mrdean05/smart-pos/images/image3.png

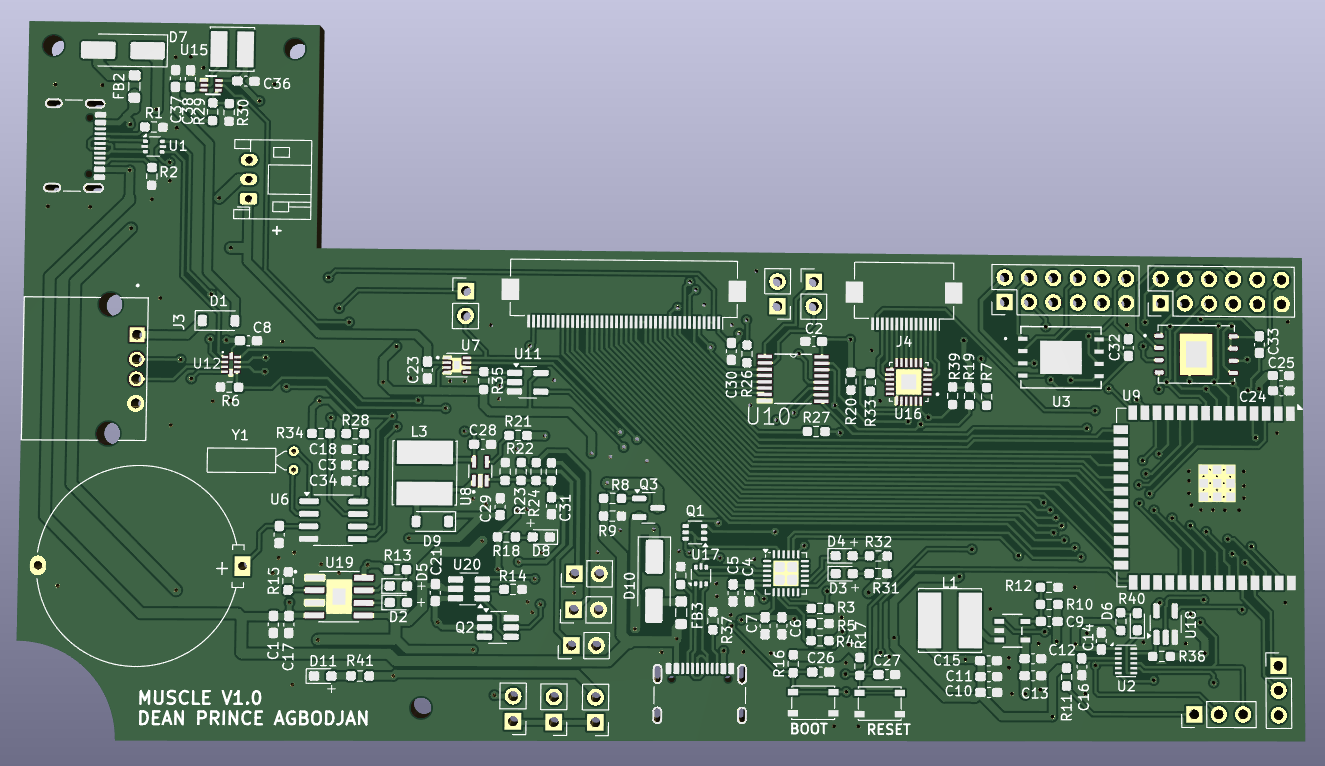
images/image3.png
