mrdean05/smart-pos/images/image5.png

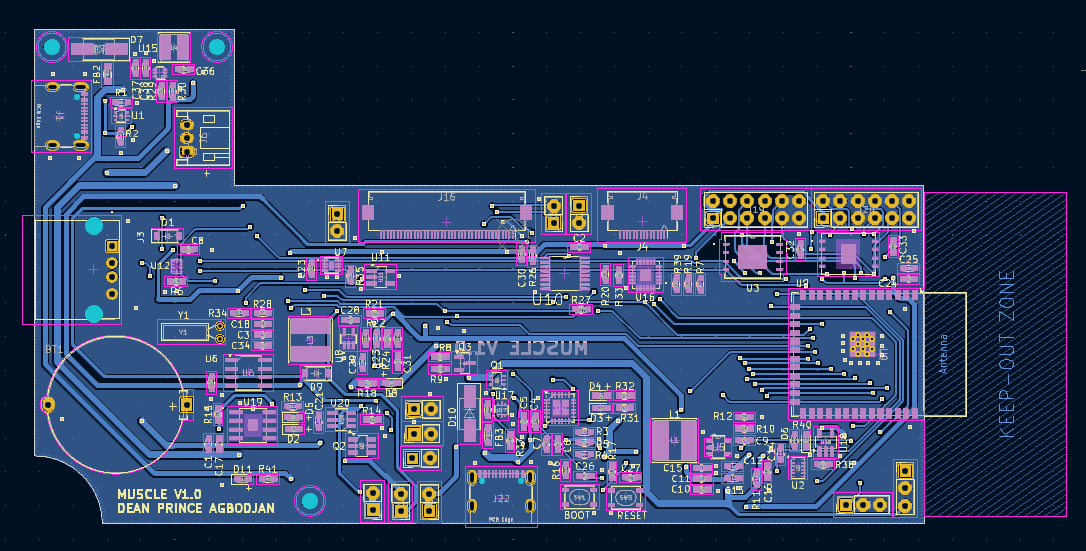
images/image5.png
